YJBeetle/3DPrintModel/BondageFiddle/Output/Right-Arch-Primary-A.3mf

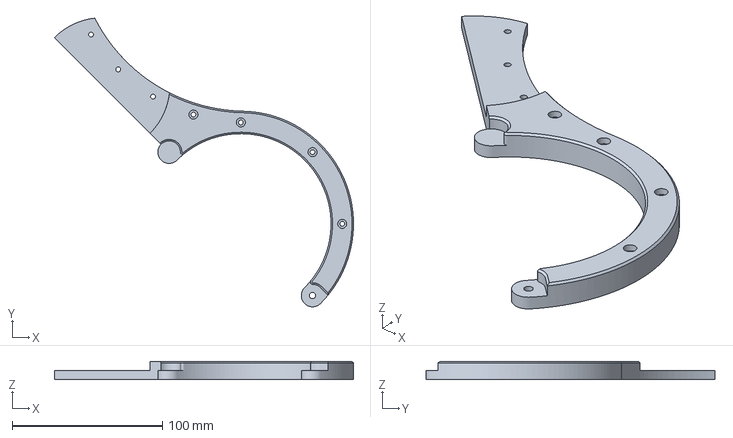
[picture p17: CAD file, 2023-12-14]
BondageFiddle/Output/Right-Arch-Primary-A.3mf
199.0 x 192.2 x 12.0 mm
