YJBeetle/3DPrintModel/BondageFiddle/Output/Test.3mf

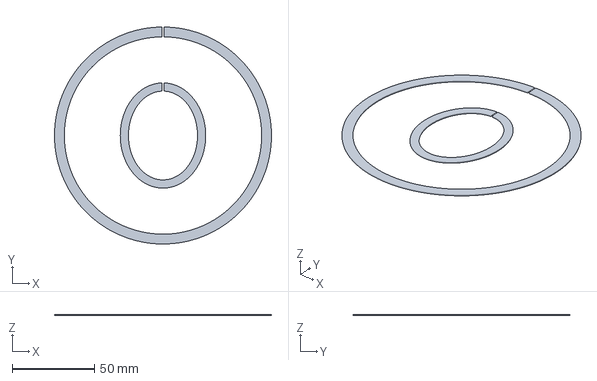
[picture p18: CAD file, 2023-12-14]
BondageFiddle/Output/Test.3mf
132.0 x 132.0 x 0.8 mm
